dushyantyadav0303/FlexKey/src/Kicad/FlexKeys.kicad_sch

## KiCad design src/Kicad/FlexKeys.kicad_sch (2026-07-21)

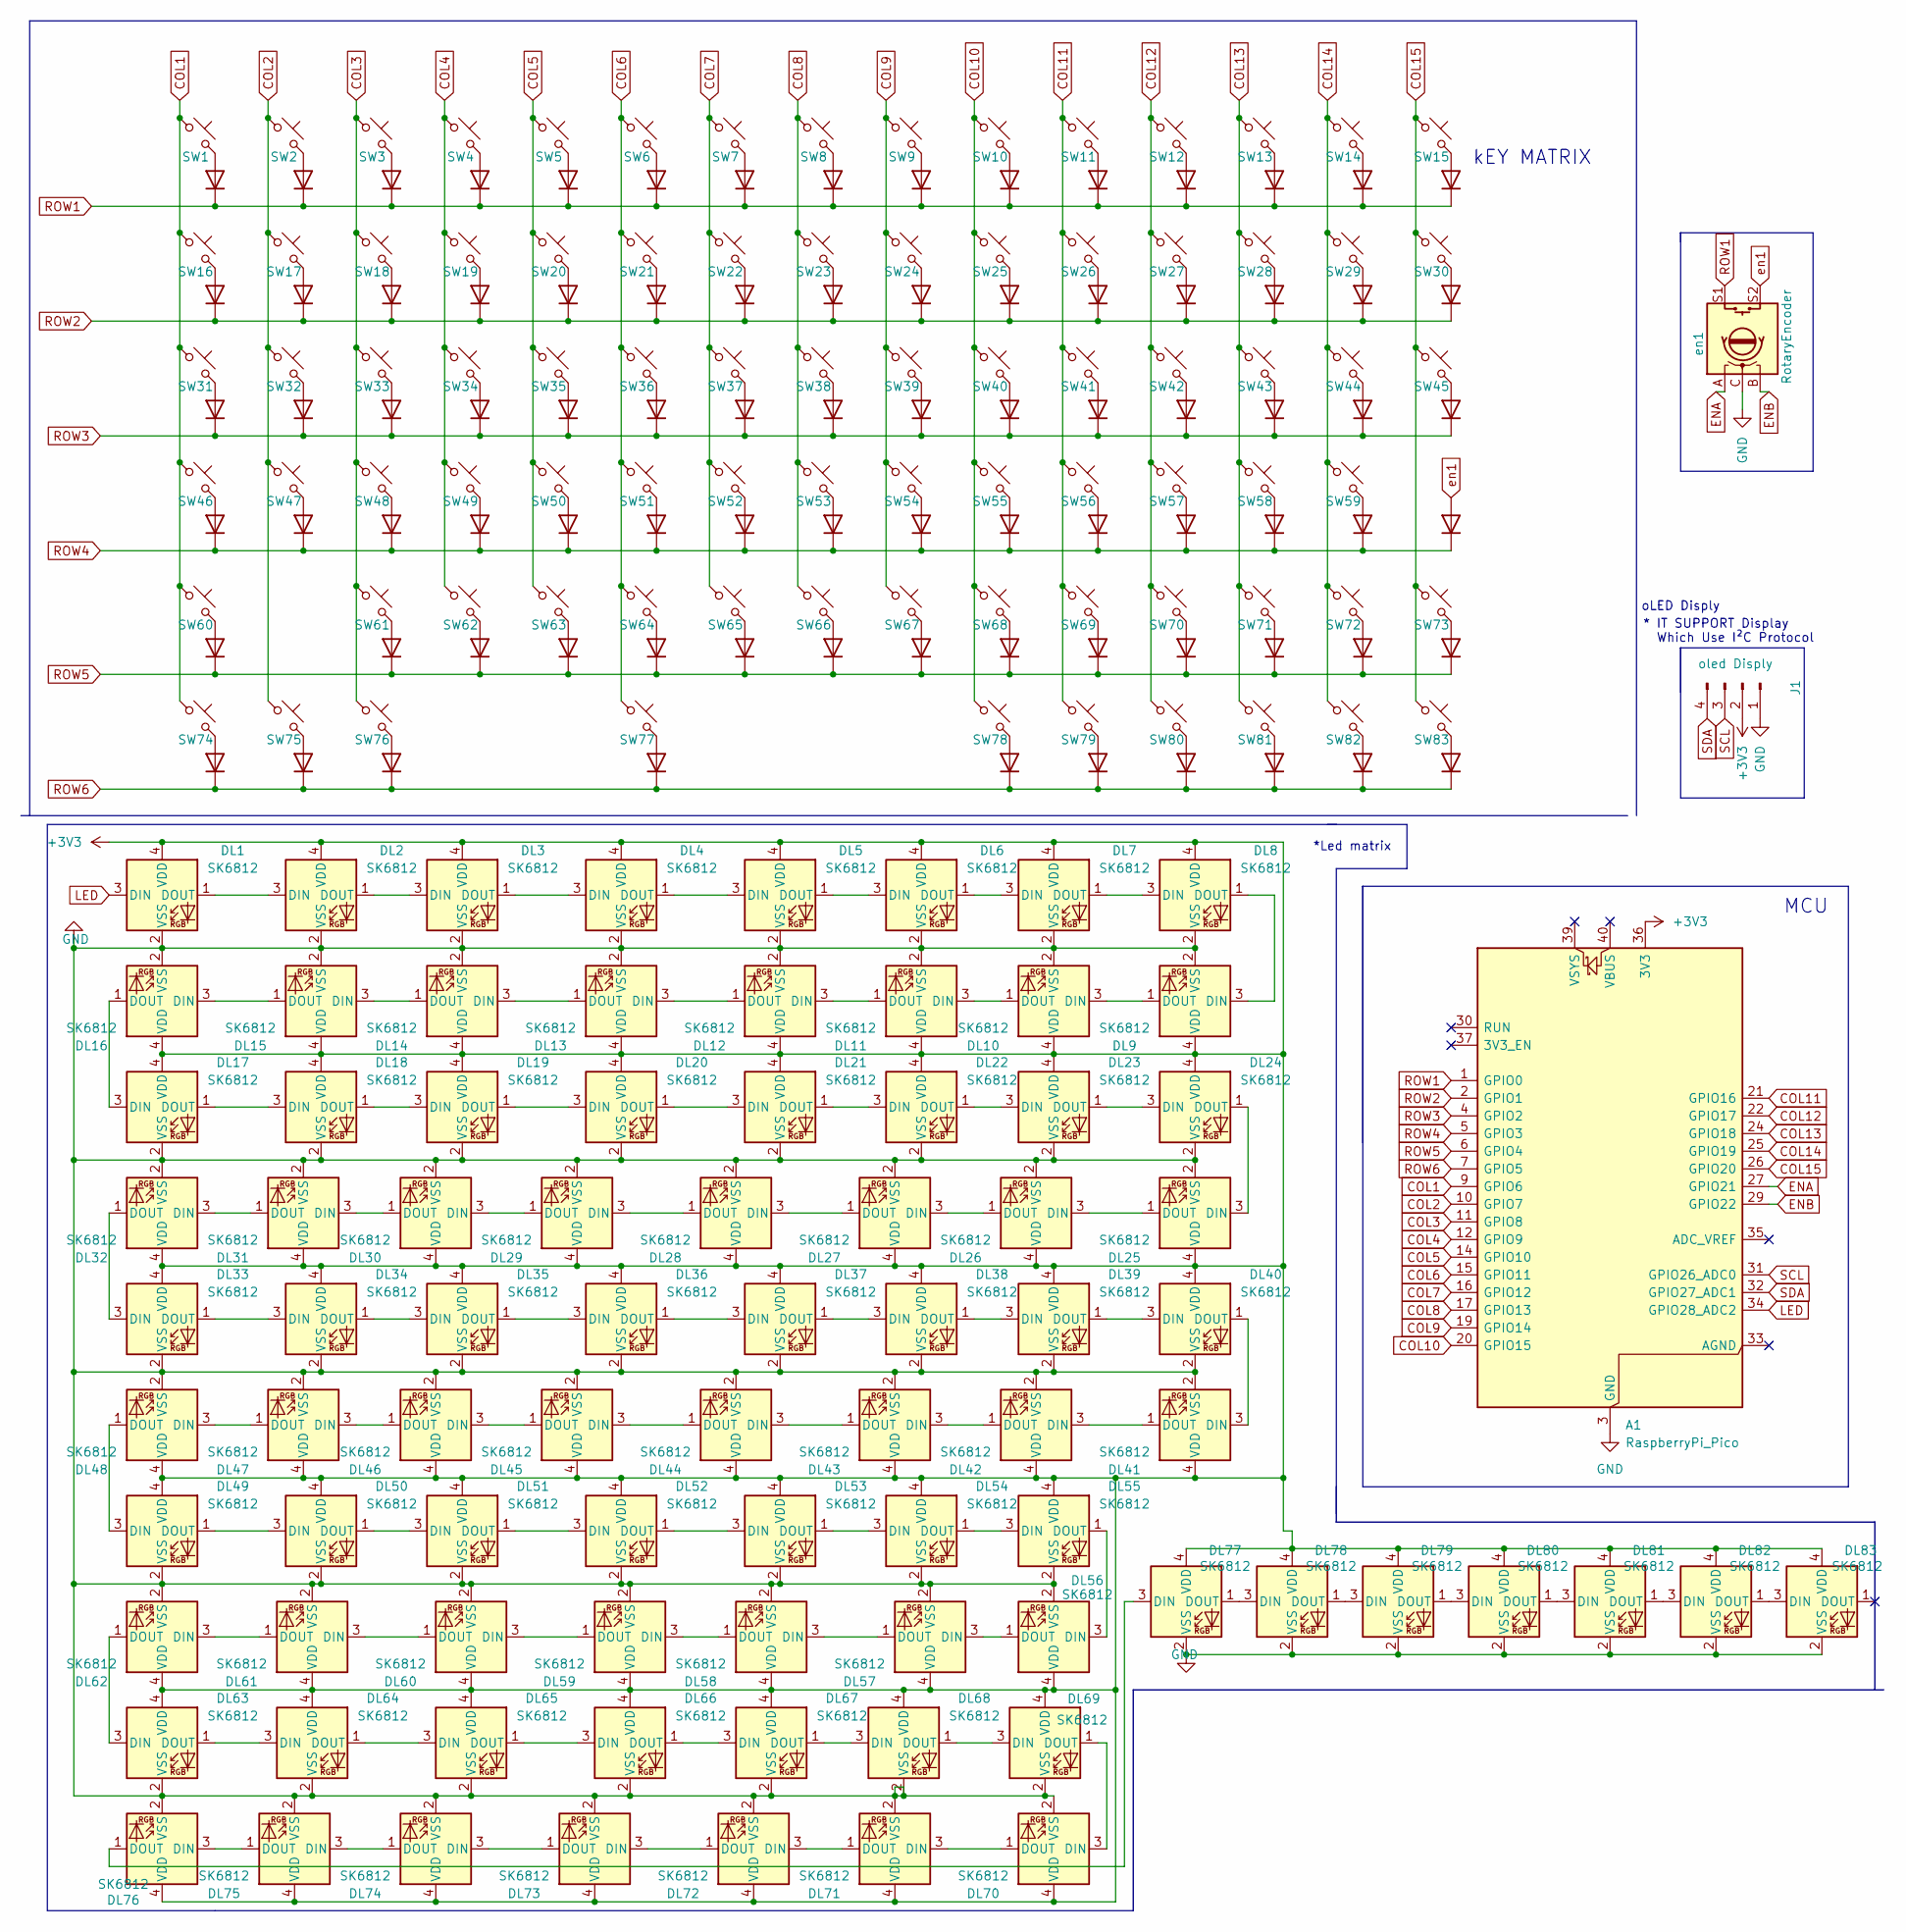
[picture p11: schematic FlexKeys.kicad_sch]

Parts:
A1: RaspberryPi_Pico; RaspberryPi_Pico_Common_Unspecified
D1, D2, D3, D4, D5, D6, D7, D8, D9, D10, D11, D12, D13, D14, D15, D16, D17, D18, D19, D20, D21, D22, D23, D24, D25, D26, D27, D28, D29, D30, D31, D32, D33, D34, D35, D36, D37, D38, D39, D40, D41, D42, D43, D44, D45, D46, D47, D48, D49, D50, D51, D52, D53, D54, D55, D56, D57, D58, D59, D60, D61, D62, D63, D64, D65, D66, D67, D68, D69, D70, D71, D72, D73, D74, D75, D76, D77, D78, D79, D80, D81, D82, D85, D86: 1N4148; D_SOD-123
DL1, DL2, DL3, DL4, DL5, DL6, DL7, DL8, DL9, DL10, DL11, DL12, DL13, DL14, DL15, DL16, DL17, DL18, DL19, DL20, DL21, DL22, DL23, DL24, DL25, DL26, DL27, DL28, DL29, DL30, DL31, DL32, DL33, DL34, DL35, DL36, DL37, DL38, DL39, DL40, DL41, DL42, DL43, DL44, DL45, DL46, DL47, DL48, DL49, DL50, DL51, DL52, DL53, DL54, DL55, DL56, DL57, DL58, DL59, DL60, DL61, DL62, DL63, DL64, DL65, DL66, DL67, DL68, DL69, DL70, DL71, DL72, DL73, DL74, DL75, DL76, DL77, DL78, DL79, DL80, DL81, DL82, DL83: SK6812; MX_SK6812MINI-E_REV
J1: oled Disply; OLED_0.91_128x32
SW1, SW2, SW3, SW4, SW5, SW6, SW7, SW8, SW9, SW10, SW11, SW12, SW13, SW14, SW15, SW16, SW17, SW18, SW19, SW20, SW21, SW22, SW23, SW24, SW25, SW26, SW27, SW28, SW29, SW30, SW31, SW32, SW33, SW34, SW35, SW36, SW37, SW38, SW39, SW40, SW41, SW42, SW43, SW44, SW45, SW46, SW47, SW48, SW49, SW50, SW51, SW52, SW53, SW54, SW55, SW56, SW57, SW58, SW59, SW60, SW61, SW62, SW63, SW64, SW65, SW66, SW67, SW68, SW69, SW70, SW71, SW72, SW73, SW74, SW75, SW76, SW77, SW78, SW79, SW80, SW81, SW82, SW83: SW_Push_45deg; MX100H
en1: RotaryEncoder; RotaryEncoder_Alps_EC11E-Switch_Vertical_H20mm

Connections:
+3V3: A1.36 (3V3), DL1.4 (VDD), DL2.4 (VDD), DL3.4 (VDD), DL4.4 (VDD), DL5.4 (VDD), DL6.4 (VDD), DL7.4 (VDD), DL8.4 (VDD), DL9.4 (VDD), DL10.4 (VDD), DL11.4 (VDD), DL12.4 (VDD), DL13.4 (VDD), DL14.4 (VDD), DL15.4 (VDD), DL16.4 (VDD), DL17.4 (VDD), DL18.4 (VDD), DL19.4 (VDD), DL20.4 (VDD), DL21.4 (VDD), DL22.4 (VDD), DL23.4 (VDD), DL24.4 (VDD), DL25.4 (VDD), DL26.4 (VDD), DL27.4 (VDD), DL28.4 (VDD), DL29.4 (VDD), DL30.4 (VDD), DL31.4 (VDD), DL32.4 (VDD), DL33.4 (VDD), DL34.4 (VDD), DL35.4 (VDD), DL36.4 (VDD), DL37.4 (VDD), DL38.4 (VDD), DL39.4 (VDD), DL40.4 (VDD), DL41.4 (VDD), DL42.4 (VDD), DL43.4 (VDD), DL44.4 (VDD), DL45.4 (VDD), DL46.4 (VDD), DL47.4 (VDD), DL48.4 (VDD), DL49.4 (VDD), DL50.4 (VDD), DL51.4 (VDD), DL52.4 (VDD), DL53.4 (VDD), DL54.4 (VDD), DL55.4 (VDD), DL56.4 (VDD), DL57.4 (VDD), DL58.4 (VDD), DL59.4 (VDD), DL60.4 (VDD), DL61.4 (VDD), DL62.4 (VDD), DL63.4 (VDD), DL64.4 (VDD), DL65.4 (VDD), DL66.4 (VDD), DL67.4 (VDD), DL68.4 (VDD), DL69.4 (VDD), DL70.4 (VDD), DL71.4 (VDD), DL72.4 (VDD), DL73.4 (VDD), DL74.4 (VDD), DL75.4 (VDD), DL76.4 (VDD), DL77.4 (VDD), DL78.4 (VDD), DL79.4 (VDD), DL80.4 (VDD), DL81.4 (VDD), DL82.4 (VDD), DL83.4 (VDD), J1.2
COL1: A1.9 (GPIO6), SW1.1, SW16.1, SW31.1, SW46.1, SW60.1, SW74.1
COL2: A1.10 (GPIO7), SW2.1, SW17.1, SW32.1, SW47.1, SW75.1
COL3: A1.11 (GPIO8), SW3.1, SW18.1, SW33.1, SW48.1, SW61.1, SW76.1
COL4: A1.12 (GPIO9), SW4.1, SW19.1, SW34.1, SW49.1, SW62.1
COL5: A1.14 (GPIO10), SW5.1, SW20.1, SW35.1, SW50.1, SW63.1
COL6: A1.15 (GPIO11), SW6.1, SW21.1, SW36.1, SW51.1, SW64.1, SW77.1
COL7: A1.16 (GPIO12), SW7.1, SW22.1, SW37.1, SW52.1, SW65.1
COL8: A1.17 (GPIO13), SW8.1, SW23.1, SW38.1, SW53.1, SW66.1
COL9: A1.19 (GPIO14), SW9.1, SW24.1, SW39.1, SW54.1, SW67.1
COL10: A1.20 (GPIO15), SW10.1, SW25.1, SW40.1, SW55.1, SW68.1, SW78.1
COL11: A1.21 (GPIO16), SW11.1, SW26.1, SW41.1, SW56.1, SW69.1, SW79.1
COL12: A1.22 (GPIO17), SW12.1, SW27.1, SW42.1, SW57.1, SW70.1, SW80.1
COL13: A1.24 (GPIO18), SW13.1, SW28.1, SW43.1, SW58.1, SW71.1, SW81.1
COL14: A1.25 (GPIO19), SW14.1, SW29.1, SW44.1, SW59.1, SW72.1, SW82.1
COL15: A1.26 (GPIO20), SW15.1, SW30.1, SW45.1, SW73.1, SW83.1
ENA: A1.27 (GPIO21), en1.A
ENB: A1.29 (GPIO22), en1.B
GND: A1.3 (GND), A1.8 (GND), A1.13 (GND), A1.18 (GND), A1.23 (GND), A1.28 (GND), A1.38 (GND), DL1.2 (VSS), DL2.2 (VSS), DL3.2 (VSS), DL4.2 (VSS), DL5.2 (VSS), DL6.2 (VSS), DL7.2 (VSS), DL8.2 (VSS), DL9.2 (VSS), DL10.2 (VSS), DL11.2 (VSS), DL12.2 (VSS), DL13.2 (VSS), DL14.2 (VSS), DL15.2 (VSS), DL16.2 (VSS), DL17.2 (VSS), DL18.2 (VSS), DL19.2 (VSS), DL20.2 (VSS), DL21.2 (VSS), DL22.2 (VSS), DL23.2 (VSS), DL24.2 (VSS), DL25.2 (VSS), DL26.2 (VSS), DL27.2 (VSS), DL28.2 (VSS), DL29.2 (VSS), DL30.2 (VSS), DL31.2 (VSS), DL32.2 (VSS), DL33.2 (VSS), DL34.2 (VSS), DL35.2 (VSS), DL36.2 (VSS), DL37.2 (VSS), DL38.2 (VSS), DL39.2 (VSS), DL40.2 (VSS), DL41.2 (VSS), DL42.2 (VSS), DL43.2 (VSS), DL44.2 (VSS), DL45.2 (VSS), DL46.2 (VSS), DL47.2 (VSS), DL48.2 (VSS), DL49.2 (VSS), DL50.2 (VSS), DL51.2 (VSS), DL52.2 (VSS), DL53.2 (VSS), DL54.2 (VSS), DL55.2 (VSS), DL56.2 (VSS), DL57.2 (VSS), DL58.2 (VSS), DL59.2 (VSS), DL60.2 (VSS), DL61.2 (VSS), DL62.2 (VSS), DL63.2 (VSS), DL64.2 (VSS), DL65.2 (VSS), DL66.2 (VSS), DL67.2 (VSS), DL68.2 (VSS), DL69.2 (VSS), DL70.2 (VSS), DL71.2 (VSS), DL72.2 (VSS), DL73.2 (VSS), DL74.2 (VSS), DL75.2 (VSS), DL76.2 (VSS), DL77.2 (VSS), DL78.2 (VSS), DL79.2 (VSS), DL80.2 (VSS), DL81.2 (VSS), DL82.2 (VSS), DL83.2 (VSS), J1.1, en1.C
LED: A1.34 (GPIO28_ADC2), DL1.3 (DIN)
unnamed: D1.2 (A), SW1.2
unnamed: D2.2 (A), SW2.2
unnamed: D3.2 (A), SW3.2
unnamed: D4.2 (A), SW4.2
unnamed: D5.2 (A), SW5.2
unnamed: D6.2 (A), SW6.2
unnamed: D7.2 (A), SW7.2
unnamed: D8.2 (A), SW8.2
unnamed: D9.2 (A), SW9.2
unnamed: D10.2 (A), SW10.2
unnamed: D11.2 (A), SW11.2
unnamed: D12.2 (A), SW12.2
unnamed: D13.2 (A), SW13.2
unnamed: D14.2 (A), SW14.2
unnamed: D15.2 (A), SW15.2
unnamed: D16.2 (A), SW16.2
unnamed: D17.2 (A), SW17.2
unnamed: D18.2 (A), SW18.2
unnamed: D19.2 (A), SW19.2
unnamed: D20.2 (A), SW20.2
unnamed: D21.2 (A), SW21.2
unnamed: D22.2 (A), SW22.2
unnamed: D23.2 (A), SW23.2
unnamed: D24.2 (A), SW24.2
unnamed: D25.2 (A), SW25.2
unnamed: D26.2 (A), SW26.2
unnamed: D27.2 (A), SW27.2
unnamed: D28.2 (A), SW28.2
unnamed: D29.2 (A), SW29.2
unnamed: D30.2 (A), SW30.2
unnamed: D31.2 (A), SW31.2
unnamed: D32.2 (A), SW32.2
unnamed: D33.2 (A), SW33.2
unnamed: D34.2 (A), SW34.2
unnamed: D35.2 (A), SW35.2
unnamed: D36.2 (A), SW36.2
unnamed: D37.2 (A), SW37.2
unnamed: D38.2 (A), SW38.2
unnamed: D39.2 (A), SW39.2
unnamed: D40.2 (A), SW40.2
unnamed: D41.2 (A), SW41.2
unnamed: D42.2 (A), SW42.2
unnamed: D43.2 (A), SW43.2
unnamed: D44.2 (A), SW44.2
unnamed: D45.2 (A), SW45.2
unnamed: D46.2 (A), SW46.2
unnamed: D47.2 (A), SW47.2
unnamed: D48.2 (A), SW48.2
unnamed: D49.2 (A), SW49.2
unnamed: D50.2 (A), SW50.2
unnamed: D51.2 (A), SW51.2
unnamed: D52.2 (A), SW52.2
unnamed: D53.2 (A), SW53.2
unnamed: D54.2 (A), SW54.2
unnamed: D55.2 (A), SW55.2
unnamed: D56.2 (A), SW56.2
unnamed: D57.2 (A), SW57.2
unnamed: D58.2 (A), SW58.2
unnamed: D59.2 (A), SW59.2
unnamed: D60.2 (A), SW60.2
unnamed: D61.2 (A), SW61.2
unnamed: D62.2 (A), SW62.2
unnamed: D63.2 (A), SW63.2
unnamed: D64.2 (A), SW64.2
unnamed: D65.2 (A), SW65.2
unnamed: D66.2 (A), SW66.2
unnamed: D67.2 (A), SW67.2
unnamed: D68.2 (A), SW68.2
unnamed: D69.2 (A), SW69.2
unnamed: D70.2 (A), SW70.2
unnamed: D71.2 (A), SW71.2
unnamed: D72.2 (A), SW72.2
unnamed: D73.2 (A), SW73.2
unnamed: D74.2 (A), SW74.2
unnamed: D75.2 (A), SW75.2
unnamed: D76.2 (A), SW76.2
unnamed: D77.2 (A), SW77.2
unnamed: D78.2 (A), SW78.2
unnamed: D79.2 (A), SW79.2
unnamed: D80.2 (A), SW80.2
unnamed: D81.2 (A), SW81.2
unnamed: D85.2 (A), SW82.2
unnamed: D86.2 (A), SW83.2
unnamed: DL1.1 (DOUT), DL2.3 (DIN)
unnamed: DL2.1 (DOUT), DL3.3 (DIN)
unnamed: DL3.1 (DOUT), DL4.3 (DIN)
unnamed: DL4.1 (DOUT), DL5.3 (DIN)
unnamed: DL5.1 (DOUT), DL6.3 (DIN)
unnamed: DL6.1 (DOUT), DL7.3 (DIN)
unnamed: DL7.1 (DOUT), DL8.3 (DIN)
unnamed: DL8.1 (DOUT), DL9.3 (DIN)
unnamed: DL10.1 (DOUT), DL11.3 (DIN)
unnamed: DL9.1 (DOUT), DL10.3 (DIN)
unnamed: DL11.1 (DOUT), DL12.3 (DIN)
unnamed: DL12.1 (DOUT), DL13.3 (DIN)
unnamed: DL13.1 (DOUT), DL14.3 (DIN)
unnamed: DL14.1 (DOUT), DL15.3 (DIN)
unnamed: DL15.1 (DOUT), DL16.3 (DIN)
unnamed: DL16.1 (DOUT), DL17.3 (DIN)
unnamed: DL17.1 (DOUT), DL18.3 (DIN)
unnamed: DL18.1 (DOUT), DL19.3 (DIN)
unnamed: DL19.1 (DOUT), DL20.3 (DIN)
unnamed: DL20.1 (DOUT), DL21.3 (DIN)
unnamed: DL21.1 (DOUT), DL22.3 (DIN)
unnamed: DL22.1 (DOUT), DL23.3 (DIN)
unnamed: DL23.1 (DOUT), DL24.3 (DIN)
unnamed: DL24.1 (DOUT), DL25.3 (DIN)
unnamed: DL25.1 (DOUT), DL26.3 (DIN)
unnamed: DL26.1 (DOUT), DL27.3 (DIN)
unnamed: DL27.1 (DOUT), DL28.3 (DIN)
unnamed: DL28.1 (DOUT), DL29.3 (DIN)
unnamed: DL29.1 (DOUT), DL30.3 (DIN)
unnamed: DL30.1 (DOUT), DL31.3 (DIN)
unnamed: DL31.1 (DOUT), DL32.3 (DIN)
unnamed: DL32.1 (DOUT), DL33.3 (DIN)
unnamed: DL33.1 (DOUT), DL34.3 (DIN)
unnamed: DL34.1 (DOUT), DL35.3 (DIN)
unnamed: DL35.1 (DOUT), DL36.3 (DIN)
unnamed: DL36.1 (DOUT), DL37.3 (DIN)
unnamed: DL37.1 (DOUT), DL38.3 (DIN)
unnamed: DL38.1 (DOUT), DL39.3 (DIN)
unnamed: DL39.1 (DOUT), DL40.3 (DIN)
unnamed: DL40.1 (DOUT), DL41.3 (DIN)
unnamed: DL41.1 (DOUT), DL42.3 (DIN)
unnamed: DL42.1 (DOUT), DL43.3 (DIN)
unnamed: DL43.1 (DOUT), DL44.3 (DIN)
unnamed: DL44.1 (DOUT), DL45.3 (DIN)
unnamed: DL45.1 (DOUT), DL46.3 (DIN)
unnamed: DL46.1 (DOUT), DL47.3 (DIN)
unnamed: DL47.1 (DOUT), DL48.3 (DIN)
unnamed: DL48.1 (DOUT), DL49.3 (DIN)
unnamed: DL49.1 (DOUT), DL50.3 (DIN)
unnamed: DL50.1 (DOUT), DL51.3 (DIN)
unnamed: DL51.1 (DOUT), DL52.3 (DIN)
unnamed: DL52.1 (DOUT), DL53.3 (DIN)
unnamed: DL53.1 (DOUT), DL54.3 (DIN)
unnamed: DL54.1 (DOUT), DL55.3 (DIN)
unnamed: DL55.1 (DOUT), DL56.3 (DIN)
unnamed: DL56.1 (DOUT), DL57.3 (DIN)
unnamed: DL57.1 (DOUT), DL58.3 (DIN)
unnamed: DL58.1 (DOUT), DL59.3 (DIN)
unnamed: DL59.1 (DOUT), DL60.3 (DIN)
unnamed: DL60.1 (DOUT), DL61.3 (DIN)
unnamed: DL61.1 (DOUT), DL62.3 (DIN)
unnamed: DL62.1 (DOUT), DL63.3 (DIN)
unnamed: DL63.1 (DOUT), DL64.3 (DIN)
unnamed: DL64.1 (DOUT), DL65.3 (DIN)
unnamed: DL65.1 (DOUT), DL66.3 (DIN)
unnamed: DL66.1 (DOUT), DL67.3 (DIN)
unnamed: DL67.1 (DOUT), DL68.3 (DIN)
unnamed: DL68.1 (DOUT), DL69.3 (DIN)
unnamed: DL69.1 (DOUT), DL70.3 (DIN)
unnamed: DL70.1 (DOUT), DL71.3 (DIN)
unnamed: DL71.1 (DOUT), DL72.3 (DIN)
unnamed: DL72.1 (DOUT), DL73.3 (DIN)
unnamed: DL73.1 (DOUT), DL74.3 (DIN)
unnamed: DL74.1 (DOUT), DL75.3 (DIN)
unnamed: DL75.1 (DOUT), DL76.3 (DIN)
unnamed: DL76.1 (DOUT), DL77.3 (DIN)
unnamed: DL77.1 (DOUT), DL78.3 (DIN)
unnamed: DL78.1 (DOUT), DL79.3 (DIN)
unnamed: DL79.1 (DOUT), DL80.3 (DIN)
unnamed: DL80.1 (DOUT), DL81.3 (DIN)
unnamed: DL81.1 (DOUT), DL82.3 (DIN)
unnamed: DL82.1 (DOUT), DL83.3 (DIN)
ROW1: A1.1 (GPIO0), D1.1 (K), D2.1 (K), D3.1 (K), D4.1 (K), D5.1 (K), D6.1 (K), D7.1 (K), D8.1 (K), D9.1 (K), D10.1 (K), D11.1 (K), D12.1 (K), D13.1 (K), D14.1 (K), D15.1 (K), en1.S1
ROW2: A1.2 (GPIO1), D16.1 (K), D17.1 (K), D18.1 (K), D19.1 (K), D20.1 (K), D21.1 (K), D22.1 (K), D23.1 (K), D24.1 (K), D25.1 (K), D26.1 (K), D27.1 (K), D28.1 (K), D29.1 (K), D30.1 (K)
ROW3: A1.4 (GPIO2), D31.1 (K), D32.1 (K), D33.1 (K), D34.1 (K), D35.1 (K), D36.1 (K), D37.1 (K), D38.1 (K), D39.1 (K), D40.1 (K), D41.1 (K), D42.1 (K), D43.1 (K), D44.1 (K), D45.1 (K)
ROW4: A1.5 (GPIO3), D46.1 (K), D47.1 (K), D48.1 (K), D49.1 (K), D50.1 (K), D51.1 (K), D52.1 (K), D53.1 (K), D54.1 (K), D55.1 (K), D56.1 (K), D57.1 (K), D58.1 (K), D59.1 (K), D82.1 (K)
ROW5: A1.6 (GPIO4), D60.1 (K), D61.1 (K), D62.1 (K), D63.1 (K), D64.1 (K), D65.1 (K), D66.1 (K), D67.1 (K), D68.1 (K), D69.1 (K), D70.1 (K), D71.1 (K), D72.1 (K), D73.1 (K)
ROW6: A1.7 (GPIO5), D74.1 (K), D75.1 (K), D76.1 (K), D77.1 (K), D78.1 (K), D79.1 (K), D80.1 (K), D81.1 (K), D85.1 (K), D86.1 (K)
SCL: A1.31 (GPIO26_ADC0), J1.3
SDA: A1.32 (GPIO27_ADC1), J1.4
en1: D82.2 (A), en1.S2

Notes on the sheet:
MCU
oLED Disply
*Led matrix
* IT SUPPORT Display
Which Use I²C Protocol
kEY MATRIX
